IA92/Scoring_Board_RF/photos/IMG_0317.JPG

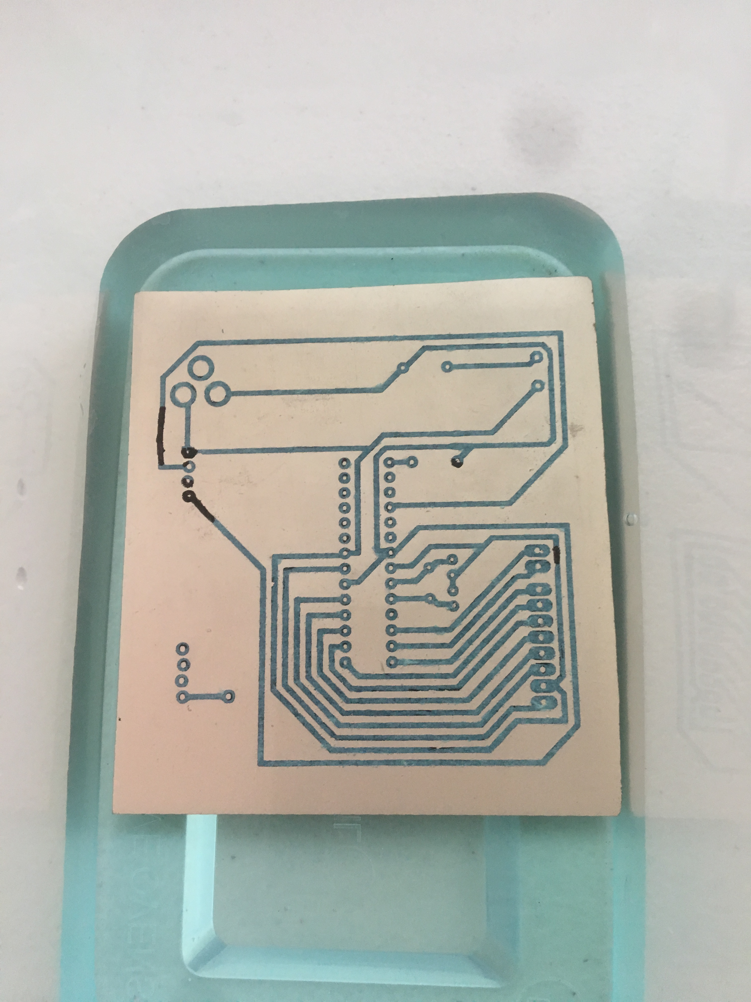
photos/IMG_0317.JPG
