IA92/Scoring_Board_RF/photos/IMG_0319.JPG

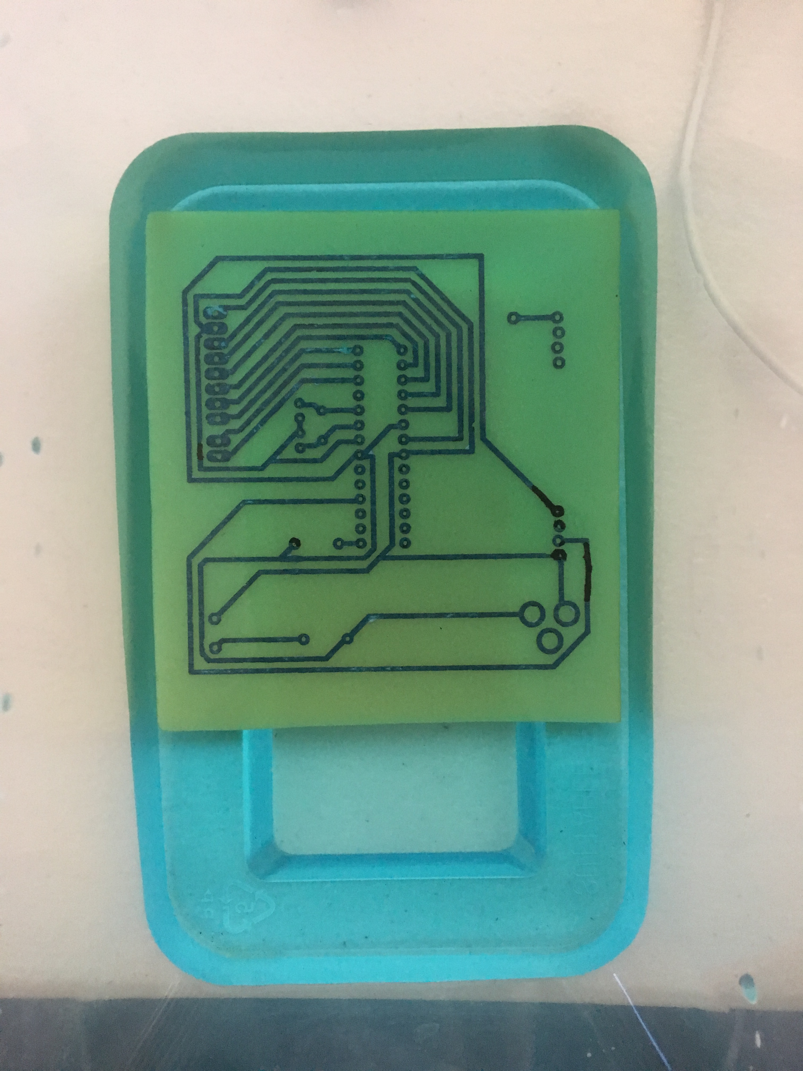
photos/IMG_0319.JPG
