IA92/Scoring_Board_RF/photos/IMG_0321.JPG

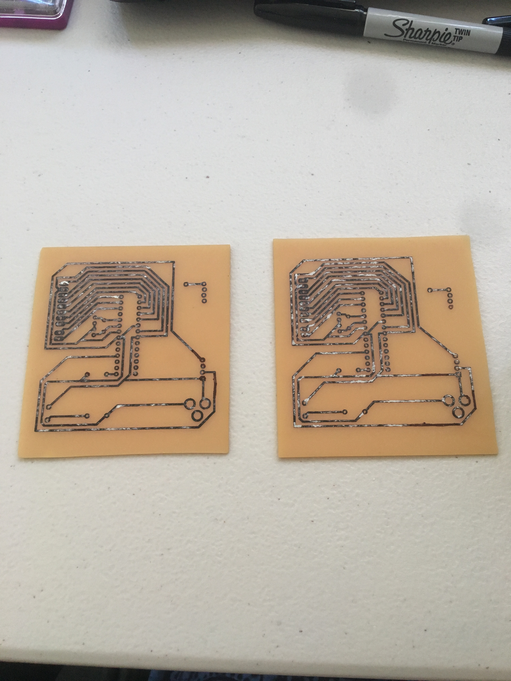
photos/IMG_0321.JPG
