IA92/Scoring_Board_RF/photos/IMG_0322.JPG

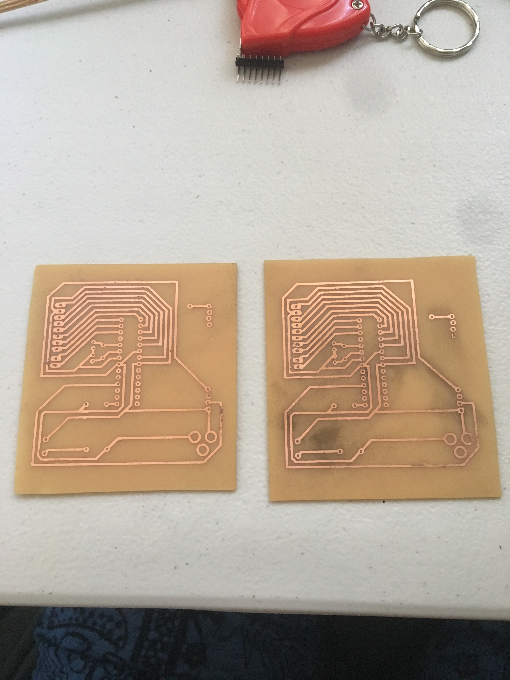
photos/IMG_0322.JPG
