IA92/Scoring_Board_RF/photos/IMG_0415.JPG

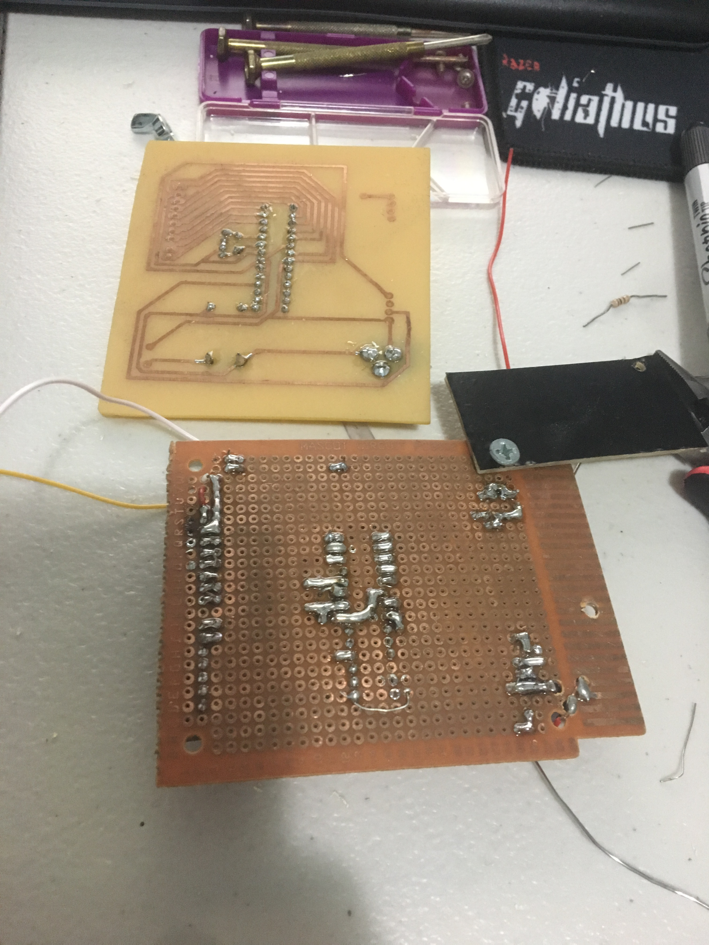
photos/IMG_0415.JPG
