IA92/Scoring_Board_RF/photos/IMG_0416.JPG

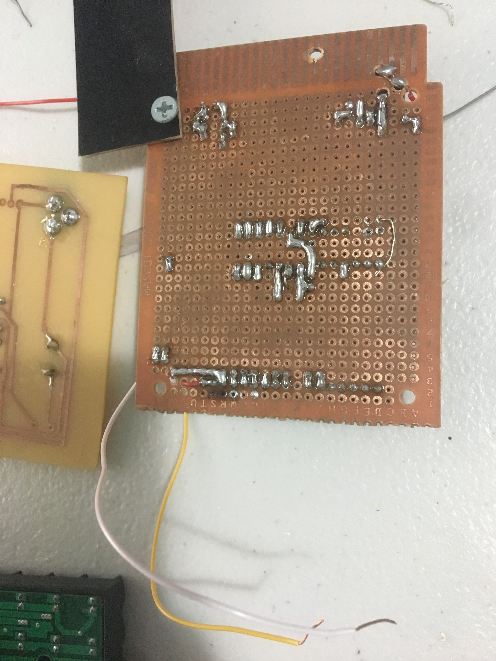
photos/IMG_0416.JPG
