IA92/Scoring_Board_RF/photos/IMG_0793.JPG

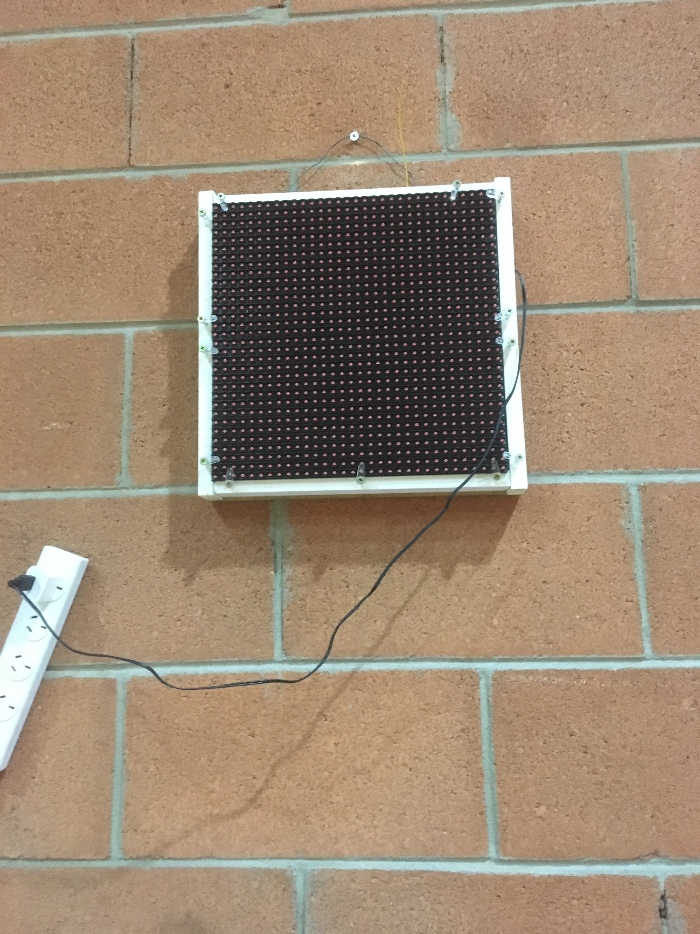
photos/IMG_0793.JPG
