IA92/Scoring_Board_RF/photos/IMG_0797.JPG

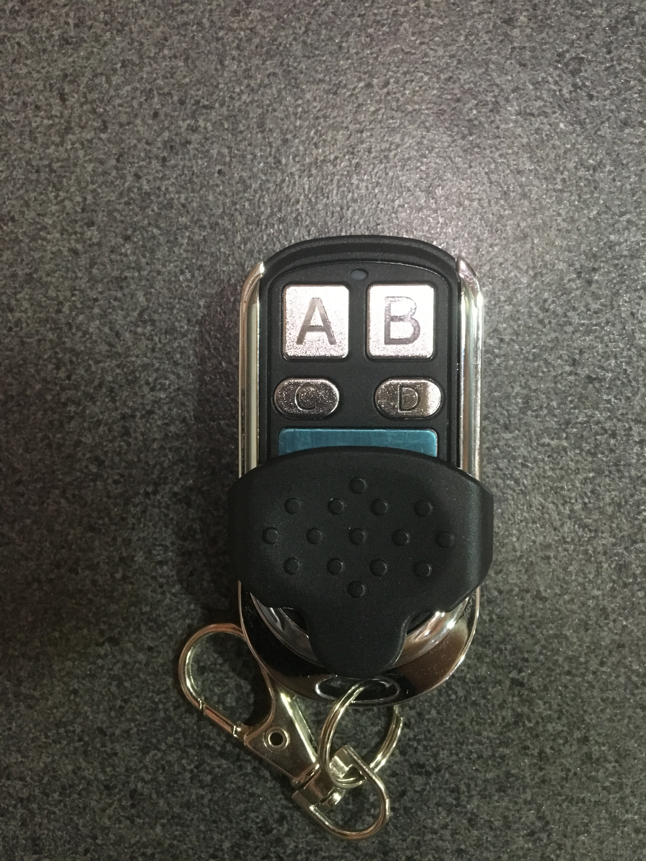
photos/IMG_0797.JPG
