IA92/Scoring_Board_RF/photos/IMG_0166.JPG

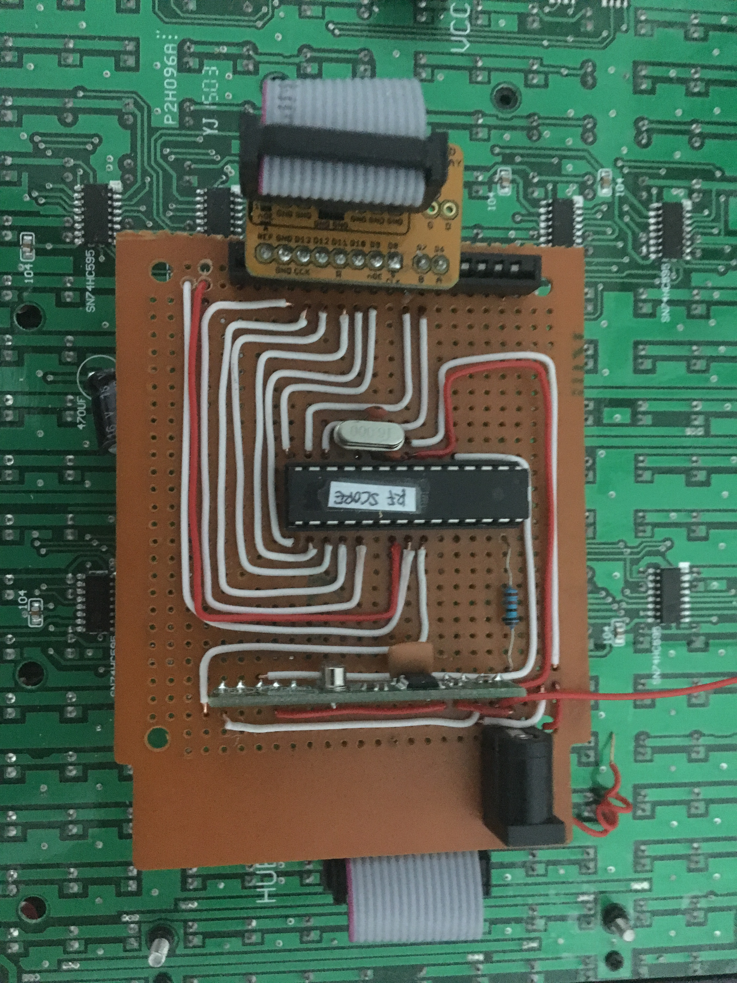
photos/IMG_0166.JPG
