IA92/Scoring_Board_RF/photos/IMG_0171.JPG

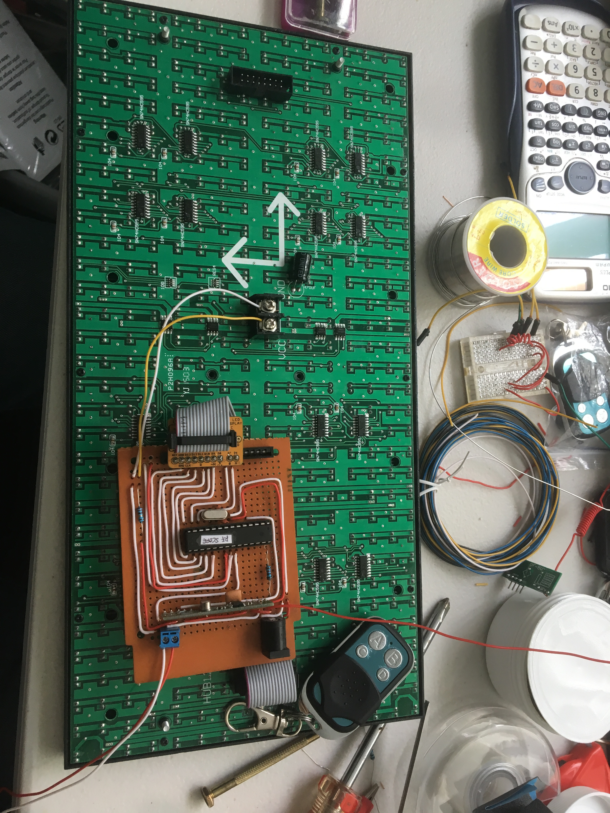
photos/IMG_0171.JPG
