IA92/Scoring_Board_RF/photos/IMG_0417.JPG

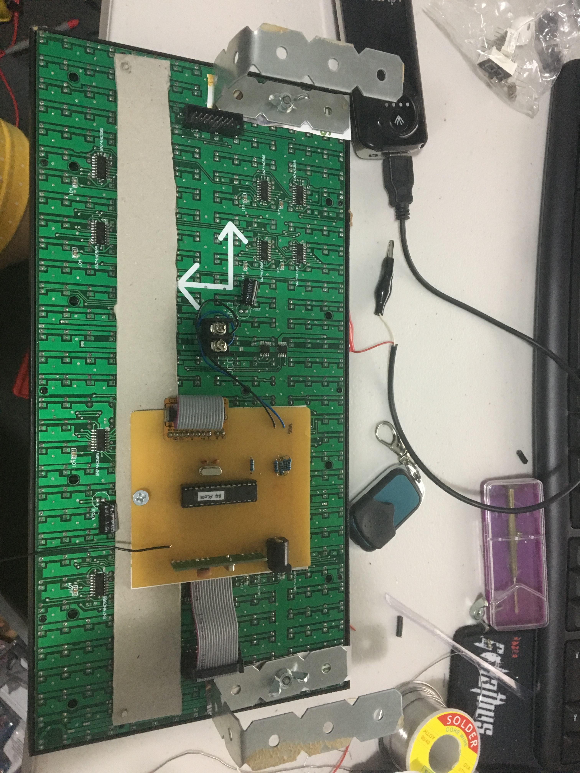
photos/IMG_0417.JPG
