IA92/Scoring_Board_RF/photos/IMG_0791.JPG

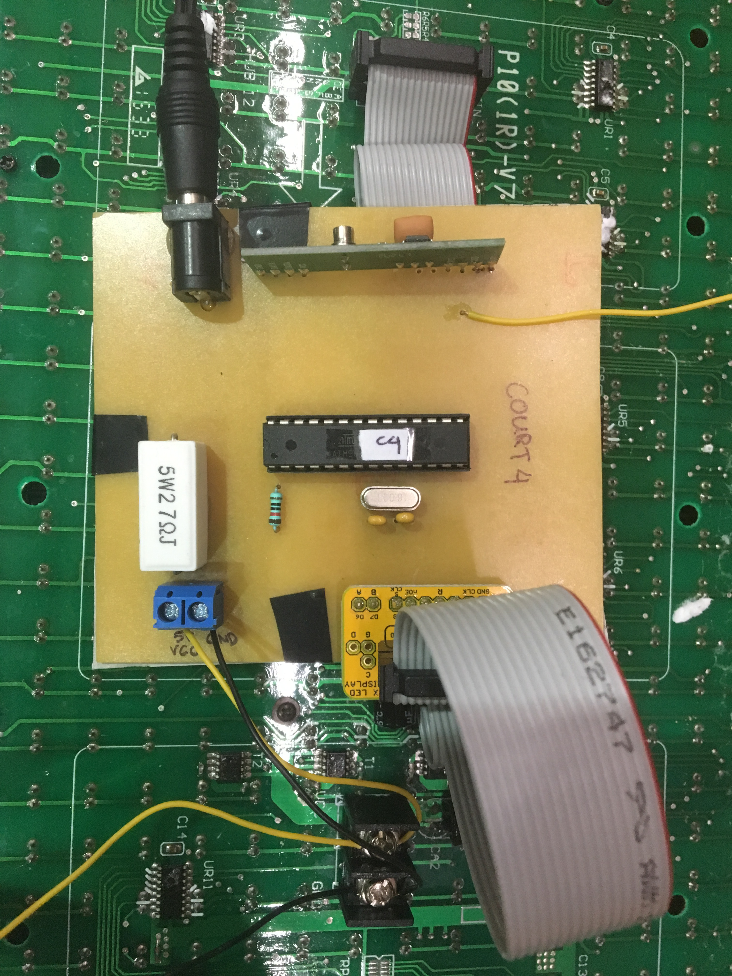
photos/IMG_0791.JPG
