IA92/Scoring_Board_RF/photos/IMG_0792.JPG

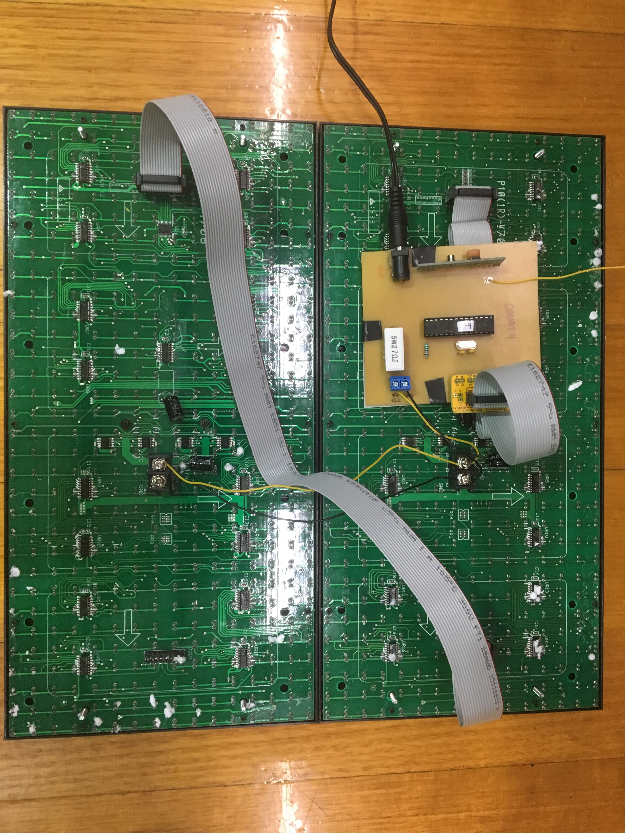
photos/IMG_0792.JPG
